jtragtenberg/TumTa/Enclosure/texturas/terra-seca-e-rachada-05555.jpg

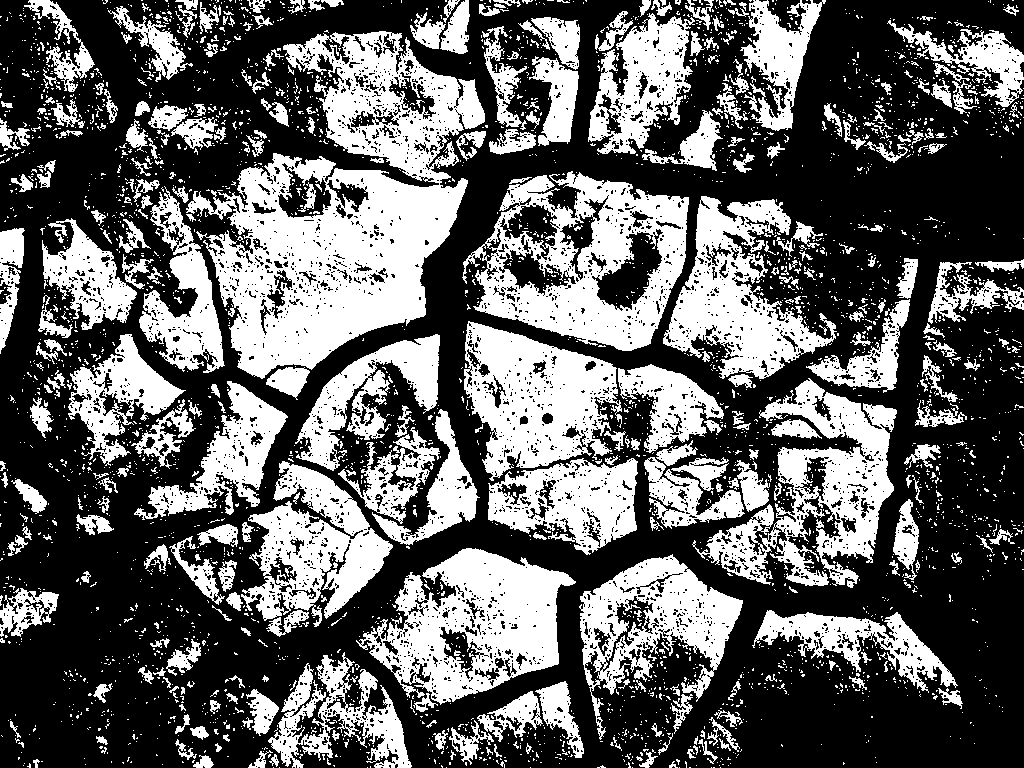
Enclosure/texturas/terra-seca-e-rachada-05555.jpg
