jtragtenberg/TumTa/Enclosure/texturas/terra.jpg

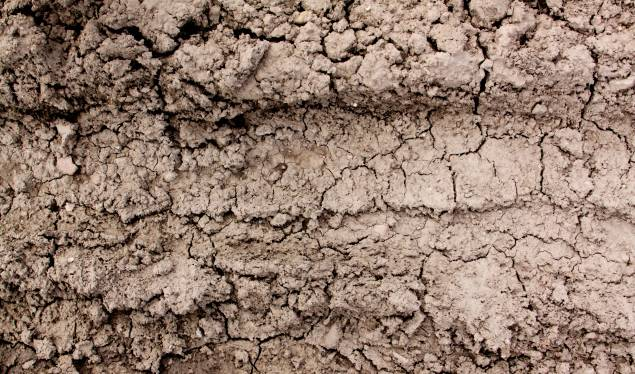
Enclosure/texturas/terra.jpg
