jtragtenberg/TumTa/Imagens/20229476_10214009757941813_3308727926528812576_o.jpg

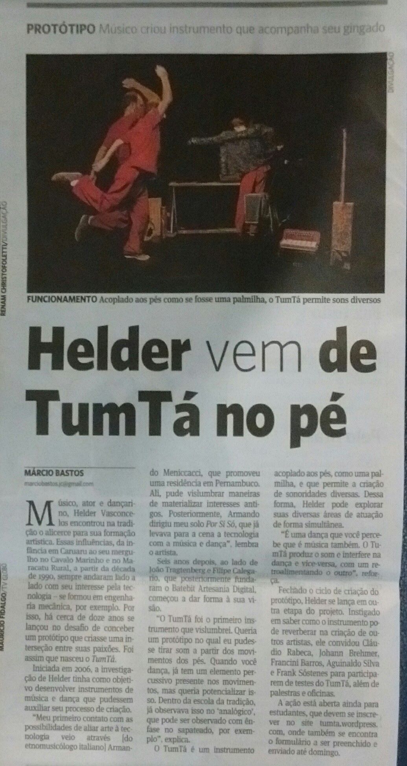
Imagens/20229476_10214009757941813_3308727926528812576_o.jpg
