jtragtenberg/TumTa/Imagens/IMG_2406.JPG

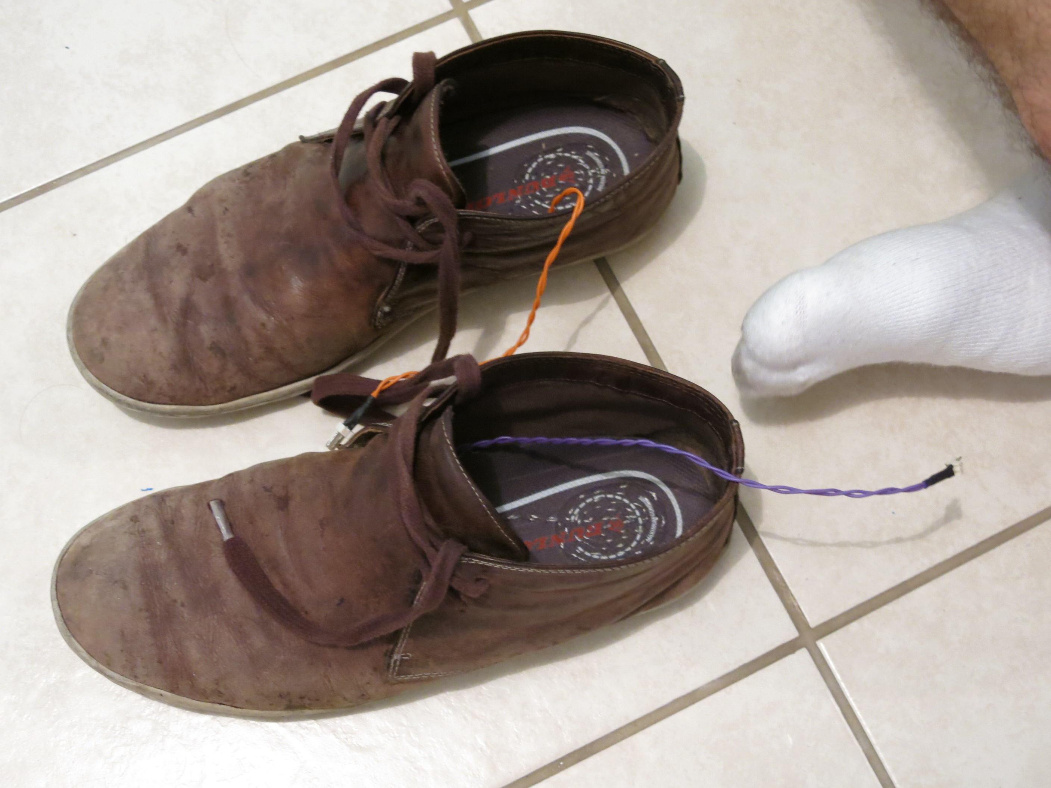
Imagens/IMG_2406.JPG
