jtragtenberg/TumTa/Imagens/IMG_2437.JPG

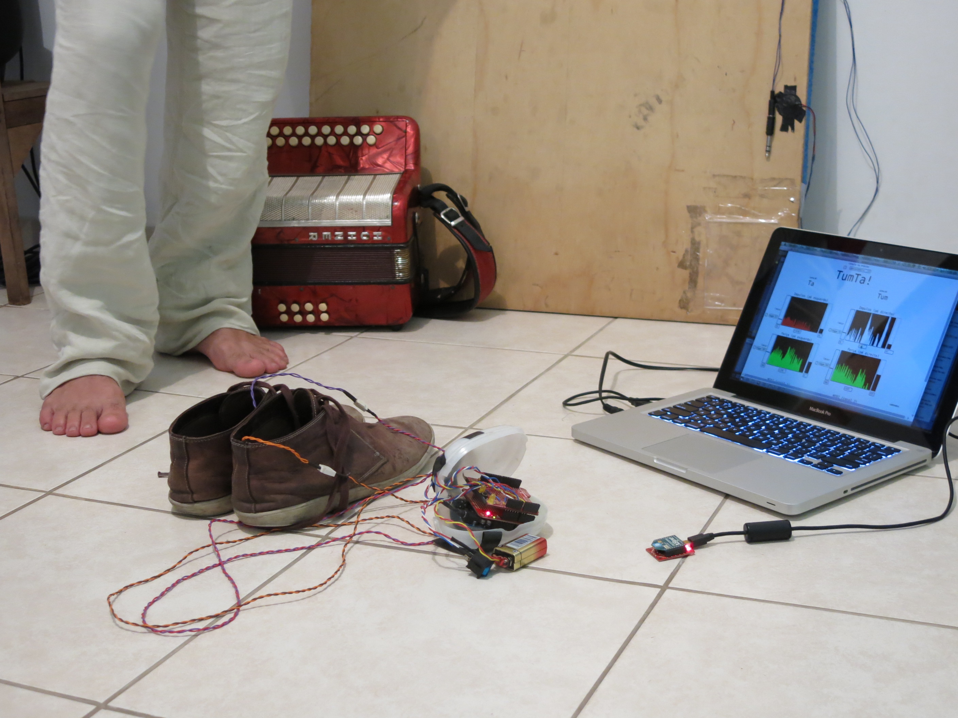
Imagens/IMG_2437.JPG
