jtragtenberg/TumTa/Imagens/IMG_2522.JPG

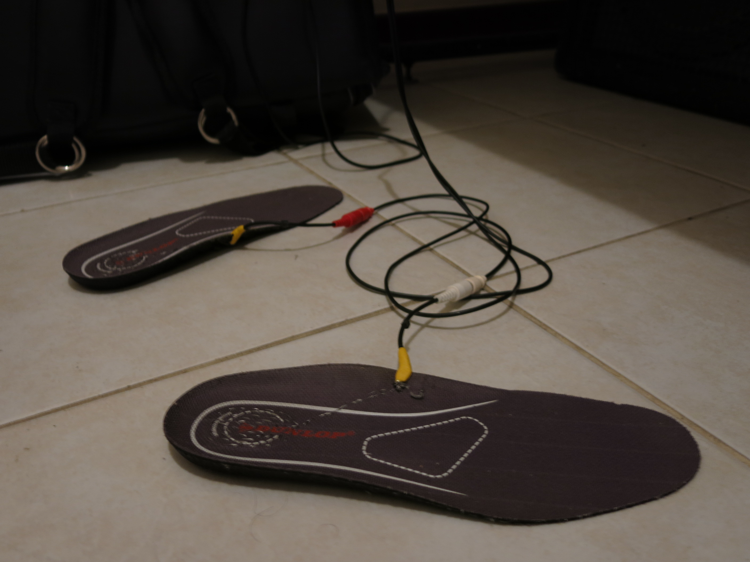
Imagens/IMG_2522.JPG
