jtragtenberg/TumTa/Imagens/tumta.png

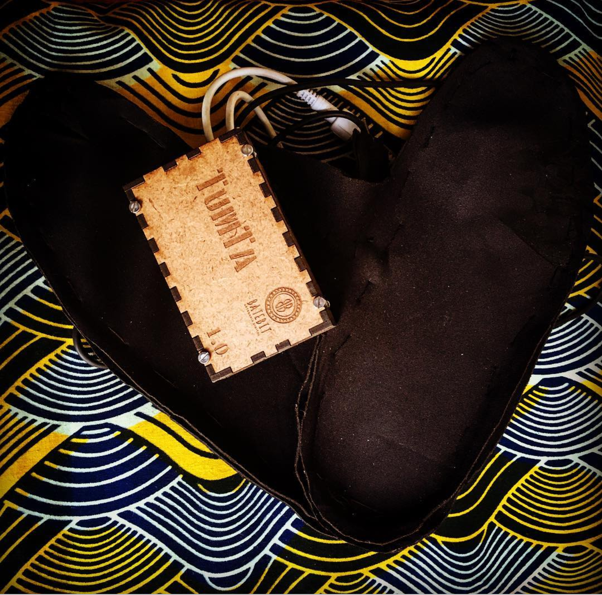
Imagens/tumta.png
