jtragtenberg/TumTa/PCB/TumTa_bot.png

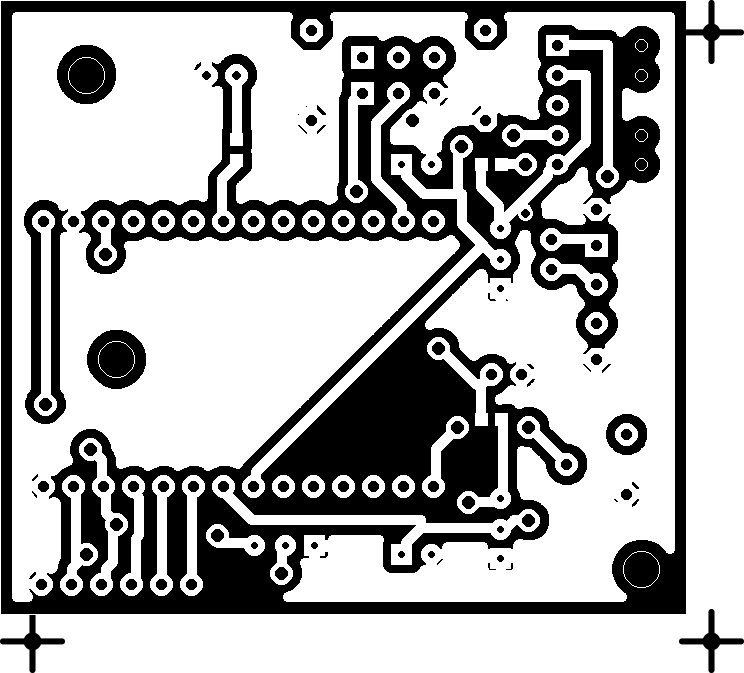
PCB/TumTa_bot.png
