jtragtenberg/TumTa/PCB/TumTa_top.png

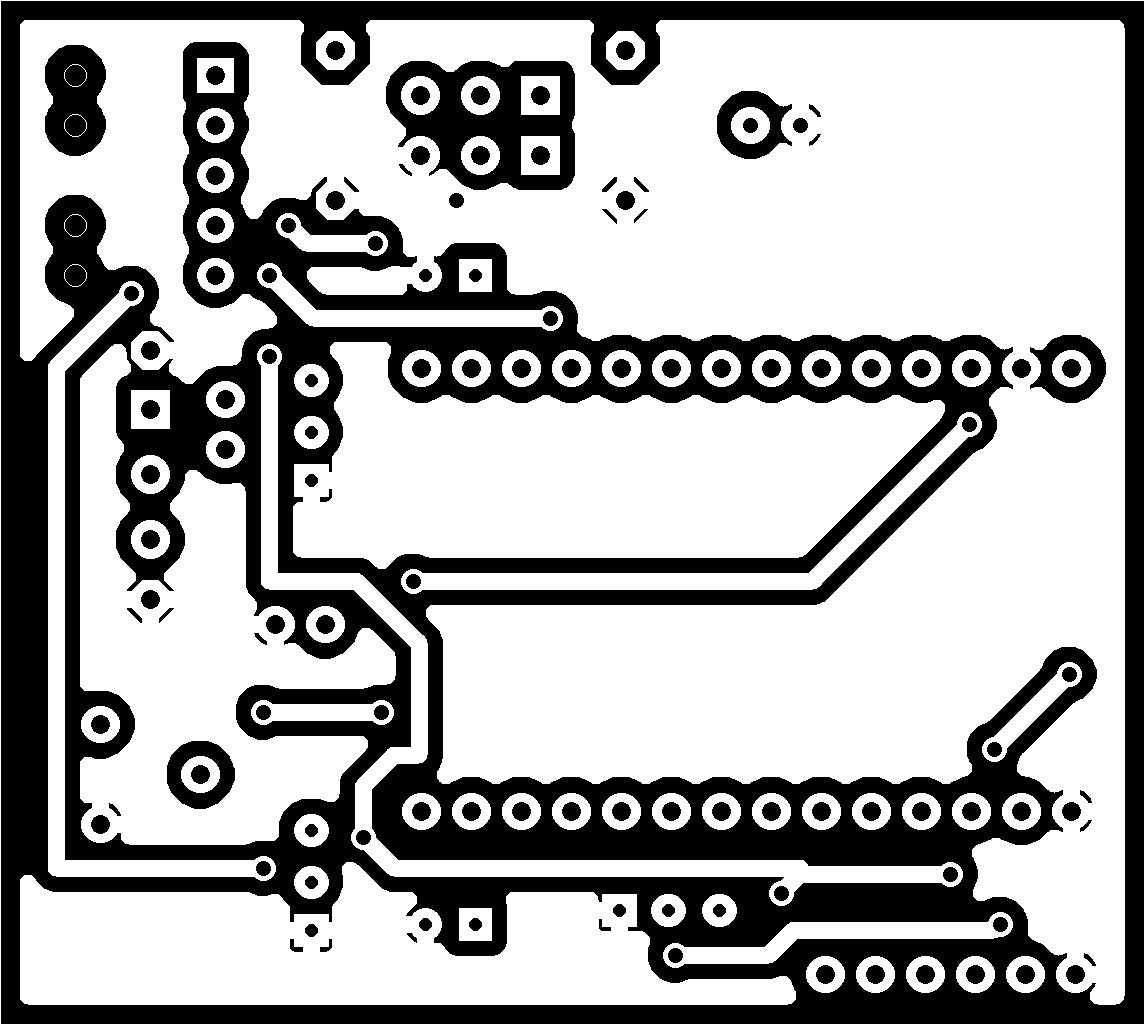
PCB/TumTa_top.png
